lochej/TimeCircuitDisplay/sw/TimeCircuitDisplay_STDIN/segments16_ascii.h

/*
 * 16segments_ascii.h
 *
 *  Created on: 15 oct. 2019
 *      Author: JLH
 */

#ifndef SEGMENTS16_ASCII_H_
#define SEGMENTS16_ASCII_H_

/*
 *  Project     Segmented LED Display - ASCII Library
 *  @author     David Madison
 *  @link       github.com/dmadison/Segmented-LED-Display-ASCII
 *  @license    MIT - Copyright (c) 2017 David Madison
 *
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
 */

/*
 *  Project     Segmented LED Display - ASCII Library
 *  @author     David Madison
 *  @link       github.com/dmadison/Segmented-LED-Display-ASCII
 *  @license    MIT - Copyright (c) 2017 David Madison
 *
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
 */

//Order MSB -> LSB
//16 Segment: DP-U-T-S-R-P-N-M-K-H-G-F-E-D-C-B-A

const uint16_t SixteenSegmentASCII[96] = {
	0x0000, /* (space) */
	0x000C, /* ! */
	0x0204, /* " */
	0xAA3C, /* # */
	0xAABB, /* $ */
	0xEE99, /* % */
	0x9371, /* & */
	0x0200, /* ' */
	0x1400, /* ( */
	0x4100, /* ) */
	0xFF00, /* * */
	0xAA00, /* + */
	0x4000, /* , */
	0x8800, /* - */
	0x1000, /* . */
	0x4400, /* / */
	0x44FF, /* 0 */
	0x040C, /* 1 */
	0x8877, /* 2 */
	0x083F, /* 3 */
	0x888C, /* 4 */
	0x90B3, /* 5 */
	0x88FB, /* 6 */
	0x000F, /* 7 */
	0x88FF, /* 8 */
	0x88BF, /* 9 */
	0x2200, /* : */
	0x4200, /* ; */
	0x9400, /* < */
	0x8830, /* = */
	0x4900, /* > */
	0x2807, /* ? */
	0x0AF7, /* @ */
	0x88CF, /* A */
	0x2A3F, /* B */
	0x00F3, /* C */
	0x223F, /* D */
	0x80F3, /* E */
	0x80C3, /* F */
	0x08FB, /* G */
	0x88CC, /* H */
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
	0x0000, /* (del) */
};


#endif /* SEGMENTS16_ASCII_H_ */
